minou65/NMEA2000-BME280/sch/NMEA2000-BME280.sch

## EAGLE design sch/NMEA2000-BME280.sch (2024-07-03)

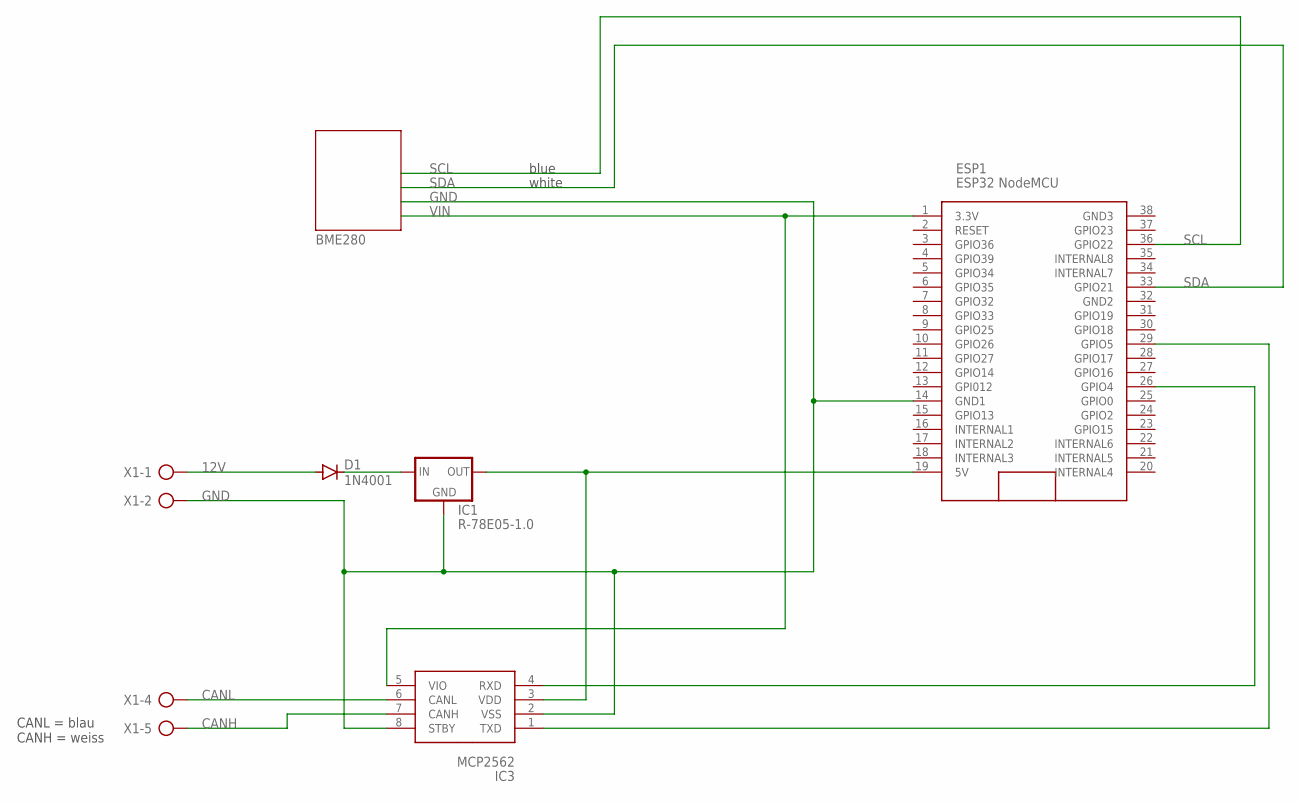
[picture p7: schematic NMEA2000-BME280.sch]

Parts:
D1: 1N4001; DO41-10
ESP1: ESP32 NodeMCU; ESP32_NODEMCU
IC1: R-78E05-1.0; 78XXS
IC3: MCP2562; DIL08
X1: AK500/5

Connections:
12V: D1.A, X1.1
CANH: IC3.7 (CANH), X1.5
CANL: IC3.6 (CANL), X1.4
GND: ESP1.14 (GND1), IC1.GND, IC3.2 (VSS), IC3.8 (STBY), X1.2
unnamed: ESP1.26 (GPIO4), IC3.4 (RXD)
unnamed: ESP1.29 (GPIO5), IC3.1 (TXD)
unnamed: ESP1.19 (5V), IC1.OUT, IC3.3 (VDD)
unnamed: D1.C, IC1.IN
SCL: ESP1.36 (GPIO22)
SDA: ESP1.33 (GPIO21)
VIN: ESP1.1 (3.3V), IC3.5 (VIO)

Notes on the sheet:
CANL = blau CANH = weiss
BME280
blue
white
