minou65/NMEA2000-BME280/src/favicon.h

// favicon.h

#ifndef _FAVICON_h
#define _FAVICON_h

#if defined(ARDUINO) && ARDUINO >= 100
	#include "arduino.h"
#else
	#include "WProgram.h"
#endif

const uint8_t favicon_ico[] PROGMEM = { // nmea2000-umwelt_96x96.png
0x89, 0x50, 0x4E, 0x47, 0x0D, 0x0A, 0x1A, 0x0A, 0x00, 0x00, 0x00, 0x0D, 0x49, 0x48, 0x44, 0x52,
0x00, 0x00, 0x00, 0x60, 0x00, 0x00, 0x00, 0x60, 0x08, 0x06, 0x00, 0x00, 0x00, 0xE2, 0x98, 0x77,
0x38, 0x00, 0x00, 0x00, 0x09, 0x70, 0x48, 0x59, 0x73, 0x00, 0x00, 0x0B, 0x13, 0x00, 0x00, 0x0B,
0x13, 0x01, 0x00, 0x9A, 0x9C, 0x18, 0x00, 0x00, 0x0E, 0xA4, 0x49, 0x44, 0x41, 0x54, 0x78, 0xDA,
0xED, 0x5D, 0x6B, 0x90, 0x54, 0xC5, 0x15, 0xFE, 0xCE, 0xBA, 0x9A, 0x15, 0xC9, 0x86, 0x18, 0xB2,
0x88, 0x04, 0x01, 0x09, 0x58, 0x29, 0x15, 0x41, 0x82, 0x10, 0x24, 0x5A, 0x04, 0x30, 0x02, 0x31,
0x15, 0x29, 0x0C, 0xC1, 0x2A, 0x83, 0x5A, 0xA0, 0x04, 0x03, 0x91, 0x40, 0x50, 0x11, 0x03, 0x04,
0x4C, 0x54, 0x7C, 0xA4, 0x30, 0x46, 0x29, 0x0D, 0xA2, 0x12, 0x04, 0x9F, 0x11, 0xD4, 0x04, 0x09,
0x20, 0x4A, 0x78, 0xC4, 0x17, 0x82, 0x80, 0x50, 0xB2, 0x80, 0x0A, 0x2B, 0x4F, 0x79, 0xB9, 0xC0,
0xBE, 0x4E, 0x7E, 0xDC, 0xAF, 0xD9, 0x43, 0xE7, 0xCE, 0x9D, 0x3B, 0xCB, 0xEE, 0xB2, 0x33, 0x3B,
0x5D, 0x75, 0xAB, 0x67, 0xCE, 0x3D, 0xDD, 0x77, 0xEE, 0x39, 0xDD, 0xA7, 0xFB, 0xBC, 0x7A, 0x44,
0x55, 0x91, 0x2D, 0x27, 0xAF, 0xE4, 0x64, 0x49, 0x90, 0x65, 0x40, 0x96, 0x01, 0xD9, 0x92, 0x65,
0x40, 0xBD, 0x2D, 0xB9, 0x71, 0x90, 0x44, 0x24, 0x17, 0xC0, 0xF5, 0x00, 0x7A, 0x02, 0xF8, 0x5A,
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
0x76, 0x37, 0x9A, 0xFB, 0x36, 0x00, 0x0D, 0xEA, 0x2D, 0x03, 0x00, 0x34, 0x30, 0x04, 0xDE, 0x01,
0xA0, 0xC0, 0xC0, 0x97, 0x9B, 0x67, 0xEC, 0x05, 0x30, 0x29, 0xEE, 0x88, 0x05, 0xD0, 0x18, 0xC0,
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
};
#endif
